chudsaviet/ntpclock/main/wifi_control.cpp

#include "wifi_control.h"

#include <string.h>
#include "freertos/FreeRTOS.h"
#include "freertos/task.h"
#include "freertos/queue.h"
#include "freertos/event_groups.h"
#include "freertos/semphr.h"
#include "esp_system.h"
#include "esp_wifi.h"
#include "esp_event.h"
#include "esp_log.h"
#include "esp_err.h"

#include "lwip/err.h"
#include "lwip/sys.h"

#include "secrets.h"

#include "unique_id.h"
#include "nvs_local.h"
#include "abort.h"

/*
    Based on 
    https://github.com/espressif/esp-idf/blob/master/examples/wifi/getting_started/station/main/station_example_main.c
*/

static EventGroupHandle_t s_wifi_event_group = NULL;

#define WIFI_CONNECTED_BIT BIT0
#define WIFI_FAIL_BIT BIT1
#define WIFI_CONTROL_TASK_LOOP_DELAY_MS 4000
#define WIFI_RESTART_TIMEOUT_SEC 900 // 15 min
#define WIFI_SHORTTERM_MAX_RETRY_COUNT 7
#define WIFI_COMMAND_QUEUE_SIZE 4
#define WIFI_CONTROL_TASK_CORE 1
#define WIFI_AP_CHANNEL 6
#define WIFI_AP_MAX_CONNECTIONS 4
#define WIFI_AP_AUTH_MODE WIFI_AUTH_WPA2_PSK
#define WPA_PASSWORD_MAX_LENGTH_CHARS 64
#define WIFI_STA_SSID_NVS_KEY "wifi_sta_ssid"
#define WIFI_STA_PASS_NVS_KEY "wifi_sta_pass"
#define WIFI_SCAN_SEMAPHORE_BLOCK_TIME_MS 120000
#define WIFI_DEFAULT_SCAN_LIST_SIZE 32
#define WIFI_CHANNEL_ACTIVE_SCAN_TIME_MIN_MS 120
#define WIFI_CHANNEL_ACTIVE_SCAN_TIME_MAX_MS 240
#define WIFI_CHANNEL_PASSIVE_SCAN_TIME_MS 360

#define HOSTNAME_TEMPLATE "ntpclock-XXXXXXXX"
#define HOSTNAME_SUFFIX_LENGTH_CHARS 8

static const char *TAG = "wifi_control.cpp";
static char hostname[sizeof HOSTNAME_TEMPLATE + 1] = {0};

static char wpaPassword[WPA_PASSWORD_MAX_LENGTH_CHARS] = {0};
static size_t wpaPasswordLength = 0;

static int s_retry_num = 0;
static timeval s_wifi_fail_timestamp = {0, 0};
static volatile bool s_wifi_failed = false;
static esp_netif_t *s_sta_netif = NULL;
static esp_netif_t *s_ap_netif = NULL;
static esp_event_handler_instance_t s_instance_any_id = NULL;
static esp_event_handler_instance_t s_instance_got_ip = NULL;

static QueueHandle_t xCommandQueue = 0;
static SemaphoreHandle_t xScanSemaphore = 0;

void vWifiSaveStaSsid(char *ssid) {
    ESP_LOGI(TAG, "Saving WiFi STA SSID <%s> to NVS.", ssid);
    l_nvs_set_str(WIFI_STA_SSID_NVS_KEY, ssid);
}

void vWifiSaveStaPass(char *pass) {
    ESP_LOGI(TAG, "Saving WiFi STA password to NVS.");
    l_nvs_set_str(WIFI_STA_PASS_NVS_KEY, pass);
}

void vPrepareStaSsidAndPass(wifi_config_t *wifi_config) {
    esp_err_t ssid_read_result = l_nvs_get_str(WIFI_STA_SSID_NVS_KEY, (char *)&wifi_config->sta.ssid, sizeof(wifi_config->sta.ssid));
    esp_err_t pass_read_result = l_nvs_get_str(WIFI_STA_PASS_NVS_KEY, (char *)&wifi_config->sta.password, sizeof(wifi_config->sta.password));

    if (ssid_read_result != ESP_OK || pass_read_result != ESP_OK) {
        strcpy((char *)wifi_config->sta.ssid, WIFI_SSID);
        strcpy((char *)wifi_config->sta.password, WIFI_PASS);
        ESP_LOGI(TAG, "WiFi STA SSID and/or password not found in NVS. Loading default values.");

        vWifiSaveStaSsid(WIFI_SSID);
        vWifiSaveStaPass(WIFI_PASS);
    } else {
        ESP_LOGI(TAG, "WiFi STA SSID and password loaded from NVS.");
    }
}

static void event_handler(void *arg, esp_event_base_t event_base,
                          int32_t event_id, void *event_data)
{
    if (event_base == WIFI_EVENT && event_id == WIFI_EVENT_STA_START)
    {
        esp_wifi_connect();
    }
    else if (event_base == WIFI_EVENT && event_id == WIFI_EVENT_STA_DISCONNECTED)
    {
        if (s_retry_num < WIFI_SHORTTERM_MAX_RETRY_COUNT)
        {
            esp_wifi_connect();
            s_retry_num++;
            ESP_LOGI(TAG, "Retry WiFi connection. Attempt: `%d`.", s_retry_num);
        }
        else
        {
            gettimeofday(&s_wifi_fail_timestamp, NULL);
            s_wifi_failed = true;
            s_retry_num = 0;
            xEventGroupSetBits(s_wifi_event_group, WIFI_FAIL_BIT);
            ESP_LOGI(TAG, "WiFi connection attempts failed.");
        }
    }
    else if (event_base == IP_EVENT && event_id == IP_EVENT_STA_GOT_IP)
    {
        ip_event_got_ip_t *event = (ip_event_got_ip_t *)event_data;
        ESP_LOGI(TAG, "Got ip:" IPSTR, IP2STR(&event->ip_info.ip));
        xEventGroupSetBits(s_wifi_event_group, WIFI_CONNECTED_BIT);
    }
}

void wifi_bits_wait()
{
    EventBits_t bits = xEventGroupWaitBits(s_wifi_event_group,
                                           WIFI_CONNECTED_BIT | WIFI_FAIL_BIT,
                                           pdFALSE,
                                           pdFALSE,
                                           portMAX_DELAY);

    if (bits & WIFI_CONNECTED_BIT)
    {
        ESP_LOGI(TAG, "Connected.");
    }
    else if (bits & WIFI_FAIL_BIT)
    {
        ESP_LOGI(TAG, "Failed to connect.");
    }
    else
    {
        ESP_LOGE(TAG, "UNEXPECTED EVENT");
    }
}

void init_hostname()
{
    uint8_t *unique_id = get_unique_id();

    memcpy((void *)&hostname, &HOSTNAME_TEMPLATE, sizeof HOSTNAME_TEMPLATE);
    for (uint8_t i = 0; i < HOSTNAME_SUFFIX_LENGTH_CHARS / 2; i++)
    {
        // Each id byte will be converted to two characters in hex.
        sprintf(
            (char *)&hostname + sizeof HOSTNAME_TEMPLATE - HOSTNAME_SUFFIX_LENGTH_CHARS + i * 2 - 1,
            "%02X",
            unique_id[i]);
    }
}

wifi_config_t xPrepareStaConfig() {
    wifi_config_t wifi_config;
    memset(&wifi_config, 0, sizeof(wifi_config));
    
    strcpy((char *)wifi_config.sta.ssid, WIFI_SSID);
    strcpy((char *)wifi_config.sta.password, WIFI_PASS);
    wifi_config.sta.threshold.authmode = WIFI_AUTH_MODE;
    wifi_config.sta.pmf_cfg.capable = true;
    wifi_config.sta.pmf_cfg.required = false;
    vPrepareStaSsidAndPass(&wifi_config);

    return wifi_config;
}

void wifi_start(void)
{
    s_sta_netif = esp_netif_create_default_wifi_sta();

    esp_netif_set_hostname(s_sta_netif, (char *)&hostname);

    wifi_init_config_t cfg = WIFI_INIT_CONFIG_DEFAULT();
    ESP_ERROR_CHECK(esp_wifi_init(&cfg));

    ESP_ERROR_CHECK(esp_event_handler_instance_register(WIFI_EVENT,
                                                        ESP_EVENT_ANY_ID,
                                                        &event_handler,
                                                        NULL,
                                                        &s_instance_any_id));
    ESP_ERROR_CHECK(esp_event_handler_instance_register(IP_EVENT,
                                                        IP_EVENT_STA_GOT_IP,
                                                        &event_handler,
                                                        NULL,
                                                        &s_instance_got_ip));

    wifi_config_t sta_config = xPrepareStaConfig();

    ESP_LOGI(TAG, "Connecting to '%s'", (char *)&sta_config.sta.ssid);

    ESP_ERROR_CHECK(esp_wifi_set_mode(WIFI_MODE_STA));
    ESP_ERROR_CHECK(esp_wifi_set_config(WIFI_IF_STA, &sta_config));
    ESP_ERROR_CHECK(esp_wifi_set_ps(WIFI_PS_MIN_MODEM));
    ESP_ERROR_CHECK_WITHOUT_ABORT(esp_wifi_start());

    ESP_LOGI(TAG, "esp_wifi_start() finished.");

    wifi_bits_wait();
}

void wifi_restart()
{
    ESP_ERROR_CHECK_WITHOUT_ABORT(esp_wifi_disconnect());
    ESP_ERROR_CHECK_WITHOUT_ABORT(esp_wifi_stop());
    ESP_ERROR_CHECK(esp_wifi_start());
    wifi_bits_wait();
}

wifi_config_t xPrepareApConfig() {
    // SSID will be equal to the hostname
    wifi_config_t wifi_config;
    memset(&wifi_config, 0, sizeof(wifi_config));
    wifi_config.ap.channel = WIFI_AP_CHANNEL;
    wifi_config.ap.max_connection = WIFI_AP_MAX_CONNECTIONS;
    wifi_config.ap.authmode = WIFI_AP_AUTH_MODE;
    wifi_config.ap.ssid_len = sizeof hostname;
    memcpy(&wifi_config.ap.ssid, &hostname, sizeof hostname);
    memcpy(&wifi_config.ap.password, &wpaPassword, wpaPasswordLength);

    return wifi_config;
}

void vSwitchToApMode()
{
    ESP_ERROR_CHECK(esp_wifi_stop());

    s_ap_netif = esp_netif_create_default_wifi_ap();

    wifi_config_t ap_config = xPrepareApConfig();
    wifi_config_t sta_config = xPrepareStaConfig();
    memset(&sta_config.sta.ssid, 0, sizeof(sta_config.sta.ssid));

    ESP_ERROR_CHECK(esp_wifi_set_mode(WIFI_MODE_APSTA));
    ESP_ERROR_CHECK(esp_wifi_set_config(WIFI_IF_AP, &ap_config));
    ESP_ERROR_CHECK(esp_wifi_set_config(WIFI_IF_STA, &sta_config));
    ESP_ERROR_CHECK(esp_wifi_start());

    ESP_LOGI(TAG, "Switching to WiFi AP mode finished. SSID: '%s', channel: %d.",
             (char *)&ap_config.ap.ssid, ap_config.ap.channel);
}

void vWifiControlTask(void *pvParameters)
{
    init_hostname();
    ESP_LOGI(TAG, "Generated hostname: %s", hostname);

    ESP_LOGI(TAG, "Starting WiFi.");
    ESP_ERROR_CHECK(esp_netif_init());

    s_wifi_event_group = xEventGroupCreate();
    ESP_ERROR_CHECK(esp_event_loop_create_default());

    wifi_start();

    for (;;)
    {

        while (uxQueueMessagesWaiting(xCommandQueue) != 0)
        {
            WifiCommandMessage message = {};
            xQueueReceive(xCommandQueue, &message, (TickType_t)0);
            switch (message.command)
            {
            case WifiCommand::SWITCH_TO_AP_MODE:
            {
                wpaPasswordLength = strlen((char *)&message.payload);
                memcpy(&wpaPassword, &message.payload, wpaPasswordLength + 1);

                ESP_LOGI(TAG, "Switching to WiFi AP mode.");
                vSwitchToApMode();
            }
            break;
            default:
                ESP_LOGE(TAG, "Unknown DisplayCommand received: %d", (uint8_t)message.command);
                abort();
                break;
            }
        }

        timeval current_timestamp = {0, 0};
        gettimeofday(&current_timestamp, NULL);

        if (s_wifi_failed &&
            current_timestamp.tv_sec - s_wifi_fail_timestamp.tv_sec >= WIFI_RESTART_TIMEOUT_SEC)
        {
            ESP_LOGI(TAG, "WiFi hard reset timeout.");
            s_wifi_failed = false;
            wifi_restart();
        };

        vTaskDelay(pdMS_TO_TICKS(WIFI_CONTROL_TASK_LOOP_DELAY_MS));
    }
    vTaskDelete(NULL);
}

void vStartWifiTask(TaskHandle_t *taskHandle, QueueHandle_t *queueHandle)
{
    xCommandQueue = xQueueCreate(WIFI_COMMAND_QUEUE_SIZE, sizeof(WifiCommandMessage));
    *queueHandle = xCommandQueue;

    xTaskCreatePinnedToCore(
        vWifiControlTask,
        "WiFi control",
        configMINIMAL_STACK_SIZE * 4,
        NULL,
        tskIDLE_PRIORITY,
        taskHandle,
        WIFI_CONTROL_TASK_CORE);
}

char *xGetWifiStaSsid()
{
    char buffer[WIFI_SSID_MAX_LEN_CHARS+1];
    memset(buffer, 0, sizeof(buffer));

    l_nvs_get_str(WIFI_STA_SSID_NVS_KEY, buffer, sizeof(buffer));
    size_t ssid_len = strlen(buffer);
    
    char *ssid = (char *)malloc(ssid_len + 1);
    memcpy(ssid, buffer, ssid_len + 1);

    return ssid;
}

int16_t usScanWifi(wifi_ap_record_t **ap_info) {
    ESP_LOGI(TAG, "Starting WiFi scan...");
    if (xScanSemaphore == 0) {
        xScanSemaphore = xSemaphoreCreateBinary();
        ESP_LOGD(TAG, "WiFi scan semaphore created.");
    } else {
        if (xSemaphoreTake(xScanSemaphore, pdMS_TO_TICKS(WIFI_SCAN_SEMAPHORE_BLOCK_TIME_MS)) == pdFALSE) {
            ESP_LOGE(TAG, "WiFi scan semphore take timeout.");
            return 0;
        }
        ESP_LOGD(TAG, "WiFi scan semaphore talken.");
    }

    uint16_t number = WIFI_DEFAULT_SCAN_LIST_SIZE;
    *ap_info = (wifi_ap_record_t *)malloc(sizeof(wifi_ap_record_t) * WIFI_DEFAULT_SCAN_LIST_SIZE);
    memset(*ap_info, 0, sizeof(wifi_ap_record_t) * WIFI_DEFAULT_SCAN_LIST_SIZE);
    uint16_t ap_count = 0;
    
    wifi_scan_config_t scan_config;
    memset(&scan_config, 0, sizeof(scan_config));
    scan_config.scan_type = WIFI_SCAN_TYPE_ACTIVE;
    scan_config.show_hidden = false;
    scan_config.scan_time.active.min = WIFI_CHANNEL_ACTIVE_SCAN_TIME_MIN_MS;
    scan_config.scan_time.active.max = WIFI_CHANNEL_ACTIVE_SCAN_TIME_MAX_MS;
    scan_config.scan_time.passive = WIFI_CHANNEL_PASSIVE_SCAN_TIME_MS;

    ESP_LOGI(TAG, "Scanning WiFi...");
    esp_err_t scan_status = esp_wifi_scan_start(&scan_config, true);
    switch (scan_status)
    {
    case ESP_OK:
        ESP_LOGI(TAG, "ESP_OK: WiFi scan succeeded.");
        break;
    case ESP_ERR_WIFI_NOT_INIT:
        ESP_LOGE(TAG, "ESP_ERR_WIFI_NOT_INIT: WiFi is not initialized by esp_wifi_init.");
        xSemaphoreGive(xScanSemaphore);
        return -1;
        break;
    case ESP_ERR_WIFI_NOT_STARTED:
        ESP_LOGE(TAG, "ESP_ERR_WIFI_NOT_STARTED: WiFi was not started by esp_wifi_start.");
        xSemaphoreGive(xScanSemaphore);
        return -1;
        break;
    case ESP_ERR_WIFI_TIMEOUT:
        ESP_LOGE(TAG, "ESP_ERR_WIFI_TIMEOUT: blocking scan timeout.");
        xSemaphoreGive(xScanSemaphore);
        return -1;
        break;
    case ESP_ERR_WIFI_STATE:
        ESP_LOGE(TAG, "ESP_ERR_WIFI_STATE: WiFi still connecting on invoking esp_wifi_scan_start.");
        xSemaphoreGive(xScanSemaphore);
        return -1;
        break;
    default:
        ESP_LOGE(TAG, "WiFi scan other error: %d.", scan_status);
        xSemaphoreGive(xScanSemaphore);
        return -1;
        break;
    }
    ESP_LOGI(TAG, "WiFi scan finished.");

    ESP_ERROR_CHECK(esp_wifi_scan_get_ap_records(&number, *ap_info));
    ESP_ERROR_CHECK(esp_wifi_scan_get_ap_num(&ap_count));
    ESP_LOGI(TAG, "Total APs scanned = %u", ap_count);
    for (int i = 0; (i < WIFI_DEFAULT_SCAN_LIST_SIZE) && (i < ap_count); i++) {
        ESP_LOGI(TAG, "SSID \t\t%s", (*ap_info)[i].ssid);
        ESP_LOGI(TAG, "RSSI \t\t%d", (*ap_info)[i].rssi);
        ESP_LOGI(TAG, "Channel \t\t%d\n", (*ap_info)[i].primary);
    }
    
    ESP_LOGD(TAG, "Giving WiFi scan semaphore.");
    xSemaphoreGive(xScanSemaphore);

    return ap_count;
}
