chudsaviet/ntpclock/include/timezone.h

#pragma once

#define TZ_NAME "America/Los_Angeles"
#define TZ_DATA_LEN 819

unsigned char PROGMEM tzData[] = {
    0x54, 0x5a, 0x69, 0x66, 0x32, 0x00, 0x00, 0x00, 0x00, 0x00, 0x00, 0x00,
    0x00, 0x00, 0x00, 0x00, 0x00, 0x00, 0x00, 0x00, 0x00, 0x00, 0x00, 0x04,
    0x00, 0x00, 0x00, 0x04, 0x00, 0x00, 0x00, 0x00, 0x00, 0x00, 0x00, 0xb9,
    0x00, 0x00, 0x00, 0x04, 0x00, 0x00, 0x00, 0x10, 0x9e, 0xa6, 0x48, 0xa0,
    0x9f, 0xbb, 0x15, 0x90, 0xa0, 0x86, 0x2a, 0xa0, 0xa1, 0x9a, 0xf7, 0x90,
    0xcb, 0x89, 0x1a, 0xa0, 0xd2, 0x23, 0xf4, 0x70, 0xd2, 0x61, 0x26, 0x10,
    0xd6, 0xfe, 0x74, 0x5c, 0xd8, 0x80, 0xad, 0x90, 0xda, 0xfe, 0xc3, 0x90,
    0xdb, 0xc0, 0x90, 0x10, 0xdc, 0xde, 0xa5, 0x90, 0xdd, 0xa9, 0xac, 0x90,
    0xde, 0xbe, 0x87, 0x90, 0xdf, 0x89, 0x8e, 0x90, 0xe0, 0x9e, 0x69, 0x90,
    0xe1, 0x69, 0x70, 0x90, 0xe2, 0x7e, 0x4b, 0x90, 0xe3, 0x49, 0x52, 0x90,
    0xe4, 0x5e, 0x2d, 0x90, 0xe5, 0x29, 0x34, 0x90, 0xe6, 0x47, 0x4a, 0x10,
    0xe7, 0x12, 0x51, 0x10, 0xe8, 0x27, 0x2c, 0x10, 0xe8, 0xf2, 0x33, 0x10,
    0xea, 0x07, 0x0e, 0x10, 0xea, 0xd2, 0x15, 0x10, 0xeb, 0xe6, 0xf0, 0x10,
    0xec, 0xb1, 0xf7, 0x10, 0xed, 0xc6, 0xd2, 0x10, 0xee, 0x91, 0xd9, 0x10,
    0xef, 0xaf, 0xee, 0x90, 0xf0, 0x71, 0xbb, 0x10, 0xf1, 0x8f, 0xd0, 0x90,
    0xf2, 0x7f, 0xc1, 0x90, 0xf3, 0x6f, 0xb2, 0x90, 0xf4, 0x5f, 0xa3, 0x90,
    0xf5, 0x4f, 0x94, 0x90, 0xf6, 0x3f, 0x85, 0x90, 0xf7, 0x2f, 0x76, 0x90,
    0xf8, 0x28, 0xa2, 0x10, 0xf9, 0x0f, 0x58, 0x90, 0xfa, 0x08, 0x84, 0x10,
    0xfa, 0xf8, 0x83, 0x20, 0xfb, 0xe8, 0x66, 0x10, 0xfc, 0xd8, 0x65, 0x20,
    0xfd, 0xc8, 0x48, 0x10, 0xfe, 0xb8, 0x47, 0x20, 0xff, 0xa8, 0x2a, 0x10,
    0x00, 0x98, 0x29, 0x20, 0x01, 0x88, 0x0c, 0x10, 0x02, 0x78, 0x0b, 0x20,
    0x03, 0x71, 0x28, 0x90, 0x04, 0x61, 0x27, 0xa0, 0x05, 0x51, 0x0a, 0x90,
    0x06, 0x41, 0x09, 0xa0, 0x07, 0x30, 0xec, 0x90, 0x07, 0x8d, 0x43, 0xa0,
    0x09, 0x10, 0xce, 0x90, 0x09, 0xad, 0xbf, 0x20, 0x0a, 0xf0, 0xb0, 0x90,
    0x0b, 0xe0, 0xaf, 0xa0, 0x0c, 0xd9, 0xcd, 0x10, 0x0d, 0xc0, 0x91, 0xa0,
    0x0e, 0xb9, 0xaf, 0x10, 0x0f, 0xa9, 0xae, 0x20, 0x10, 0x99, 0x91, 0x10,
    0x11, 0x89, 0x90, 0x20, 0x12, 0x79, 0x73, 0x10, 0x13, 0x69, 0x72, 0x20,
    0x14, 0x59, 0x55, 0x10, 0x15, 0x49, 0x54, 0x20, 0x16, 0x39, 0x37, 0x10,
    0x17, 0x29, 0x36, 0x20, 0x18, 0x22, 0x53, 0x90, 0x19, 0x09, 0x18, 0x20,
    0x1a, 0x02, 0x35, 0x90, 0x1a, 0xf2, 0x34, 0xa0, 0x1b, 0xe2, 0x17, 0x90,
    0x1c, 0xd2, 0x16, 0xa0, 0x1d, 0xc1, 0xf9, 0x90, 0x1e, 0xb1, 0xf8, 0xa0,
    0x1f, 0xa1, 0xdb, 0x90, 0x20, 0x76, 0x2b, 0x20, 0x21, 0x81, 0xbd, 0x90,
    0x22, 0x56, 0x0d, 0x20, 0x23, 0x6a, 0xda, 0x10, 0x24, 0x35, 0xef, 0x20,
    0x25, 0x4a, 0xbc, 0x10, 0x26, 0x15, 0xd1, 0x20, 0x27, 0x2a, 0x9e, 0x10,
    0x27, 0xfe, 0xed, 0xa0, 0x29, 0x0a, 0x80, 0x10, 0x29, 0xde, 0xcf, 0xa0,
    0x2a, 0xea, 0x62, 0x10, 0x2b, 0xbe, 0xb1, 0xa0, 0x2c, 0xd3, 0x7e, 0x90,
    0x2d, 0x9e, 0x93, 0xa0, 0x2e, 0xb3, 0x60, 0x90, 0x2f, 0x7e, 0x75, 0xa0,
    0x30, 0x93, 0x42, 0x90, 0x31, 0x67, 0x92, 0x20, 0x32, 0x73, 0x24, 0x90,
    0x33, 0x47, 0x74, 0x20, 0x34, 0x53, 0x06, 0x90, 0x35, 0x27, 0x56, 0x20,
    0x36, 0x32, 0xe8, 0x90, 0x37, 0x07, 0x38, 0x20, 0x38, 0x1c, 0x05, 0x10,
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
