chudsaviet/ntpclock/main/unique_id.cpp

#include "unique_id.h"

#include <esp_log.h>
#include <esp_system.h>
#include <nvs.h>
#include <nvs_flash.h>
#include <sha/sha_parallel_engine.h>

#include "abort.h"
#include "nvs_local.h"

#define TAG "unique_id.cpp"

uint8_t global_unique_id[UNIQUE_ID_SIZE_BYTES];

/*
    Generate new unique ID.
    The problem here is that ESP32 MAC addresses are not unique.
    They are set per silicon batch.
    Parameters:
        output - 20 bytes buffer.
*/
void generate_unique_id(uint8_t *output)
{
    // Set uniqueness base size equal to hash block size.
    // Just because.
    uint8_t uniqueness_base[SHA1_BLOCK_SIZE_BYTES] = {};

    // Fill first 8 bytes with base MAC address.
    ESP_LOGI(TAG, "Reading base MAC address from EFUSE BLK0.");
    esp_err_t ret = ESP_OK;
    ret = esp_efuse_mac_get_default(uniqueness_base);
    if (ret != ESP_OK)
    {
        ESP_LOGE(TAG, "Failed to get base MAC address. (%s)", esp_err_to_name(ret));
        delayed_abort();
    }
    else
    {
        ESP_LOGI(TAG, "Base MAC Address read.");
    }

    // Fill the rest with pseudo random values.
    // We just need high degree of uniqueness here, not unpredictability, so pseudo random is ok.
    ESP_LOGI(TAG, "Generating random bytes.");
    esp_fill_random((uint8_t *)&uniqueness_base + MAC_ADDRESS_SIZE_BYTES, SHA1_BLOCK_SIZE_BYTES - MAC_ADDRESS_SIZE_BYTES);

    // Calculate SHA1 hash of the uniqueness_base.
    ESP_LOGI(TAG, "Calculating SHA1.");
    esp_sha(SHA1, (uint8_t *)&uniqueness_base, sizeof uniqueness_base, output);
}

void log_unique_id(uint8_t *unique_id)
{
    char *s = (char *)malloc(UNIQUE_ID_SIZE_BYTES * 2 + 1);
    for (size_t i = 0; i < UNIQUE_ID_SIZE_BYTES; i++)
    {
        sprintf(s + i * 2, "%02x", unique_id[i]);
    }

    ESP_LOGI(TAG, "Unique ID: %s", s);
    free(s);
}

esp_err_t load_unique_id_from_nvs(uint8_t *output)
{
    ESP_LOGI(TAG, "Reading unique ID from NVS...");
    return l_nvs_get_array(UNIQUE_ID_NVS_KEY, (void *)&global_unique_id, UNIQUE_ID_SIZE_BYTES);
}

void save_unique_id_to_nvs(uint8_t *unique_id)
{
    ESP_LOGI(TAG, "Saving Unique ID to NVS.");
    l_nvs_set_array(UNIQUE_ID_NVS_KEY, (void *)global_unique_id, UNIQUE_ID_SIZE_BYTES);
}

void init_unique_id()
{
    esp_err_t ret = load_unique_id_from_nvs((uint8_t *)&global_unique_id);
    if (ret != ESP_OK)
    {
        ESP_LOGI(TAG, "No unique ID found in NVS, generating new one.");
        generate_unique_id((uint8_t *)&global_unique_id);
        save_unique_id_to_nvs((uint8_t *)&global_unique_id);
    }
    else
    {
        ESP_LOGI(TAG, "Unique ID loaded from NVS.");
    }
    log_unique_id((uint8_t *)&global_unique_id);
}

uint8_t *get_unique_id()
{
    return (uint8_t *)global_unique_id;
}
