chudsaviet/ntpclock/include/wifi.h

#pragma once

#include <Arduino.h>
#include <SPI.h>
#include <WiFiNINA.h>

#include "secrets.h"

bool wifiBegin();

void wifiLowPower();
void wifiNoLowPower();

// You won't be able to begin again if you call end.
void wifiEnd();
bool wifiConnect();
void wifiDisconnect();
bool wifiReconnect();
